pietwauters/esp32_scoring_device_hardware/images/pcb/rev1.2x/img101.jpg

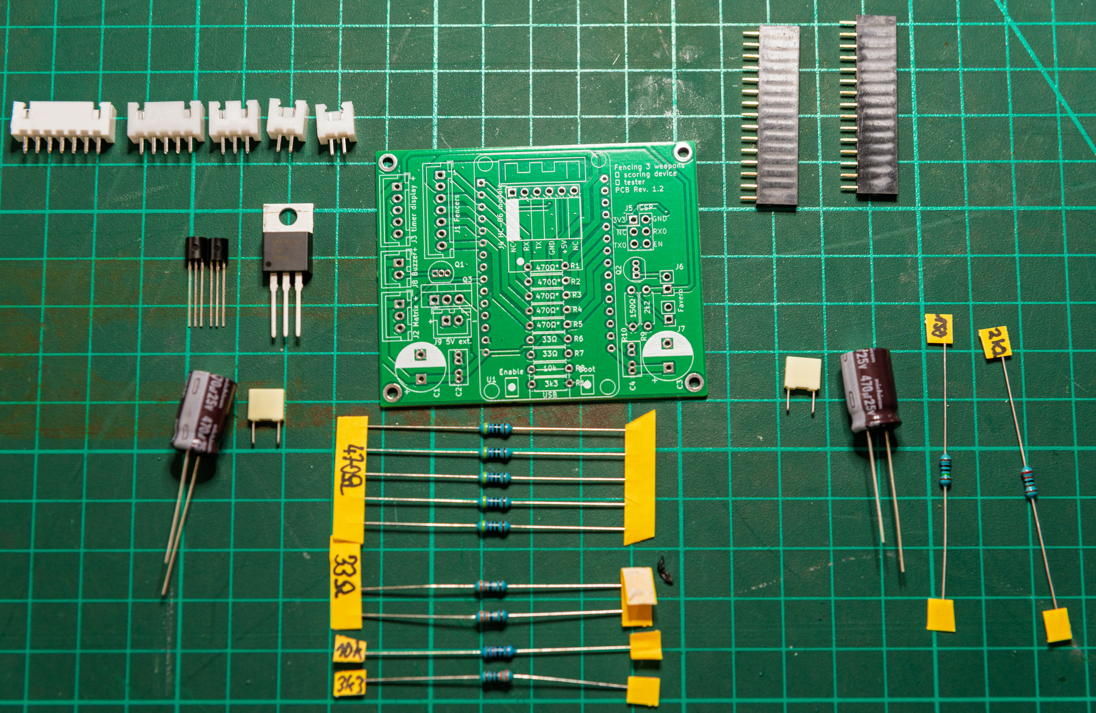
images/pcb/rev1.2x/img101.jpg
