pietwauters/esp32_scoring_device_hardware/images/pcb/rev1.2x/img102.jpg

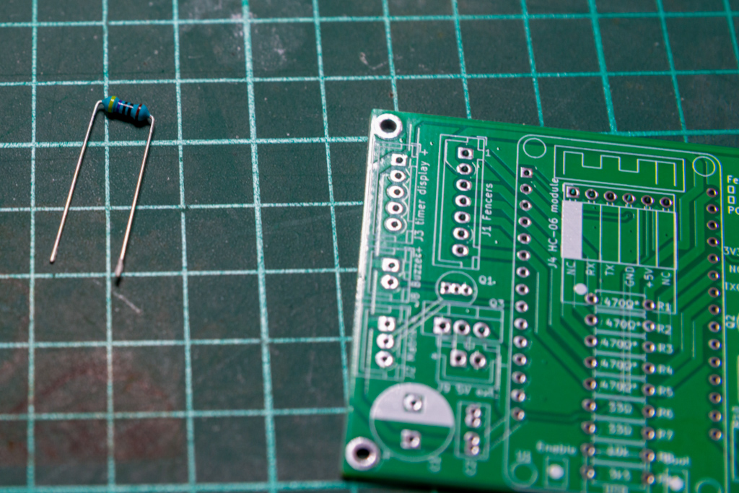
images/pcb/rev1.2x/img102.jpg
